bvidotto/ESP32-Monitor-Light/images/bar.webp

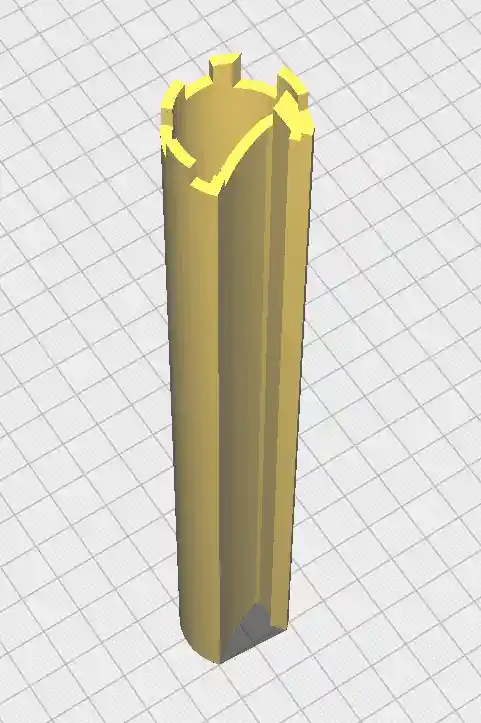
images/bar.webp
